dword1511/stm32-vserprog/boards/stm32-vserprog-v3.h

#ifndef __BOARD_H__
#define __BOARD_H__

#include <stdbool.h>
#include <libopencm3/stm32/rcc.h>
#include <libopencm3/stm32/gpio.h>

/*
 * Board definitions for STM32 VSerprog V3
 * Eagle files are in the "pcb" folder.
 */

#define BOARD_USE_DEBUG_PINS_AS_GPIO true /* We have to disable JTAG / SWD to access PA13 */

#define BOARD_RCC_LED                RCC_GPIOA
#define BOARD_PORT_LED               GPIOA
#define BOARD_PIN_LED                GPIO0
#define BOARD_LED_HIGH_IS_BUSY       true

#define BOARD_RCC_USB_PULLUP         RCC_GPIOA
#define BOARD_PORT_USB_PULLUP        GPIOA
#define BOARD_PIN_USB_PULLUP         GPIO13
#define BOARD_USB_HIGH_IS_PULLUP     true

/* Currently you can only use SPI1, since it has highest clock. */

#endif /* __BOARD_H__ */
